Sebski123/WordClock/TestMatrixDisplay/TestMatrixDisplay.ino

//We always have to include the library
#include "LedControl.h"

/*
 Now we need a LedControl to work with.
 ***** These pin numbers will probably not work with your hardware *****
 pin 12 is connected to the DataIn 
 pin 11 is connected to the CLK 
 pin 10 is connected to LOAD 
 We have only a single MAX72XX.
 */
LedControl lc=LedControl(14,16,15,4);

/* we always wait a bit between updates of the display */
unsigned long delaytime=100;

void setup() {

  Serial.begin(9600);
  /*
   The MAX72XX is in power-saving mode on startup,
   we have to do a wakeup call
   */
  lc.shutdown(0,false);
  /* Set the brightness to a medium values */
  lc.setIntensity(0,8);
  /* and clear the display */
  lc.clearDisplay(0);
}

/* 
 This function will light up every Led on the matrix.
*/
void single() {
  for(int row=0;row<8;row++) {
    for(int col=0;col<8;col++) {
      delay(delaytime);
      lc.setLed(0,row,col,true);
      Serial.print(row);
      Serial.print("\t");
      Serial.println(col);
      delay(delaytime);
    }
  }
}

void loop() { 
  single();
}
